Murwnas/psvsd-2040/assets/stop-motion/1.png

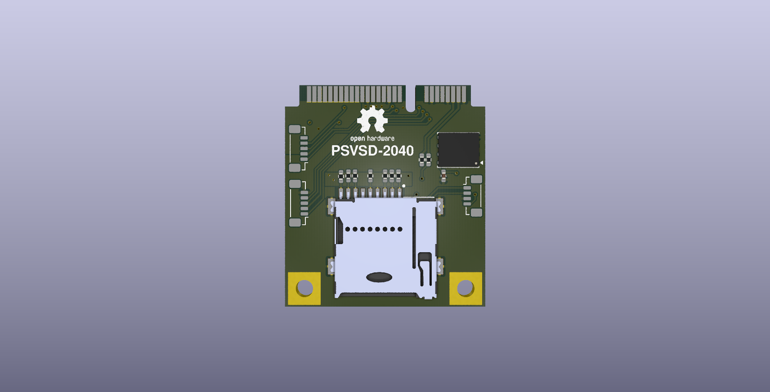
assets/stop-motion/1.png
