Murwnas/psvsd-2040/assets/stop-motion/7.png

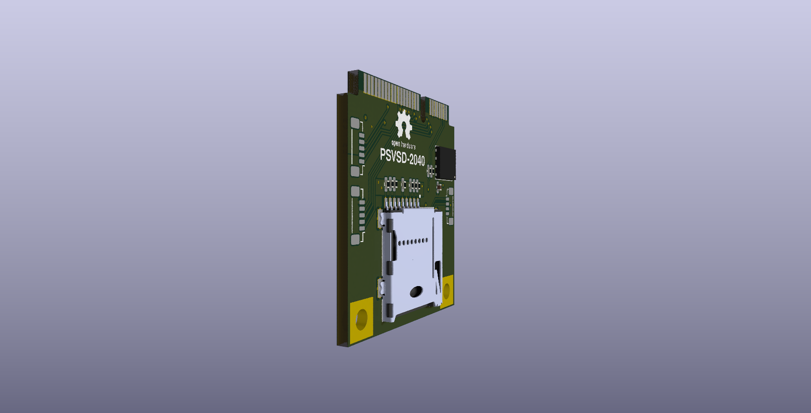
assets/stop-motion/7.png
