Murwnas/psvsd-2040/assets/stop-motion/8.png

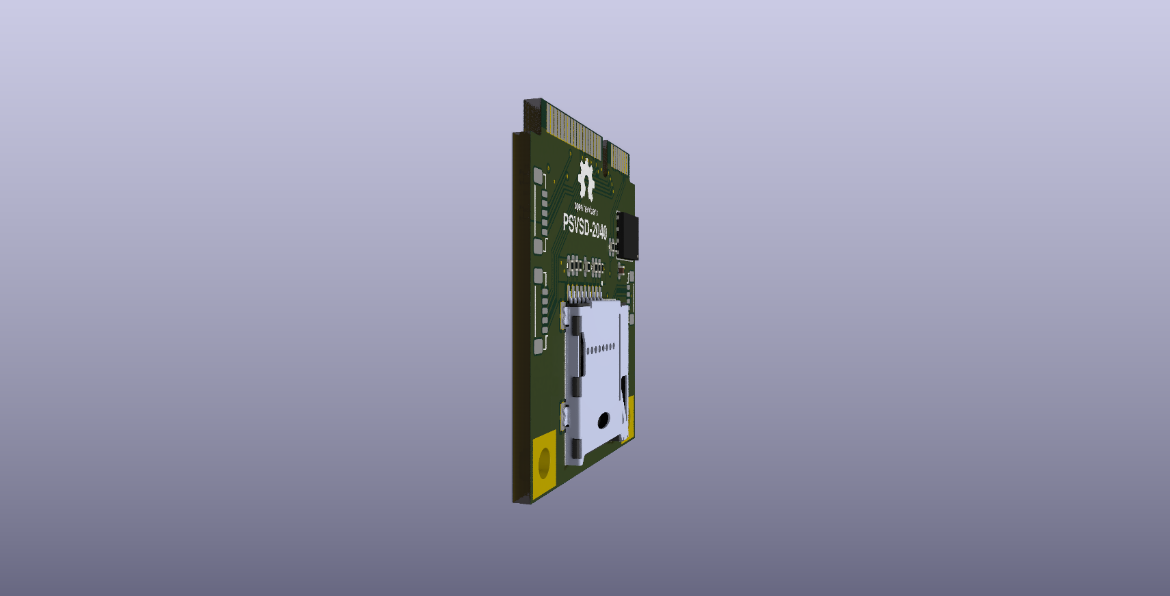
assets/stop-motion/8.png
