Murwnas/psvsd-2040/assets/stop-motion/13.png

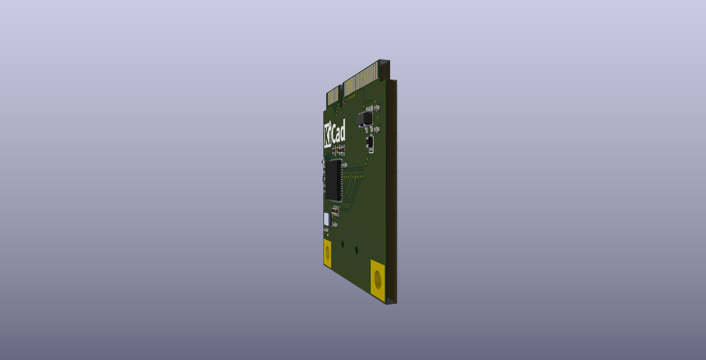
assets/stop-motion/13.png
